Laya-21/XIMO_2.0/Media/img1.jpg

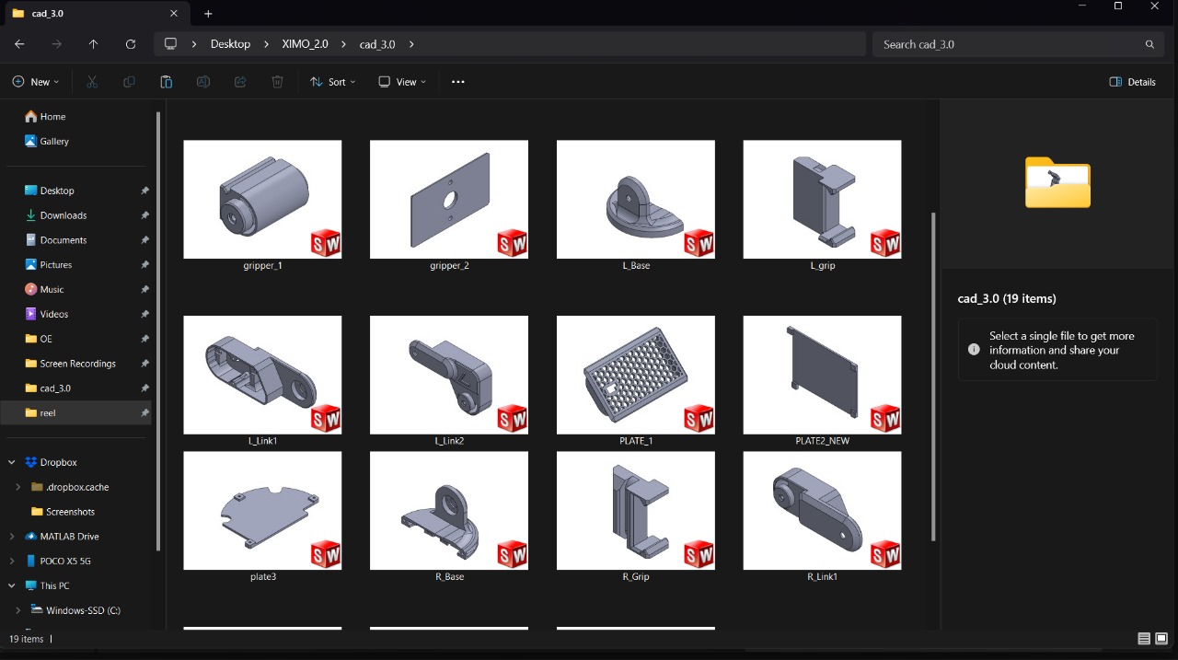
Media/img1.jpg
