Laya-21/XIMO_2.0/Media/img3.jpg

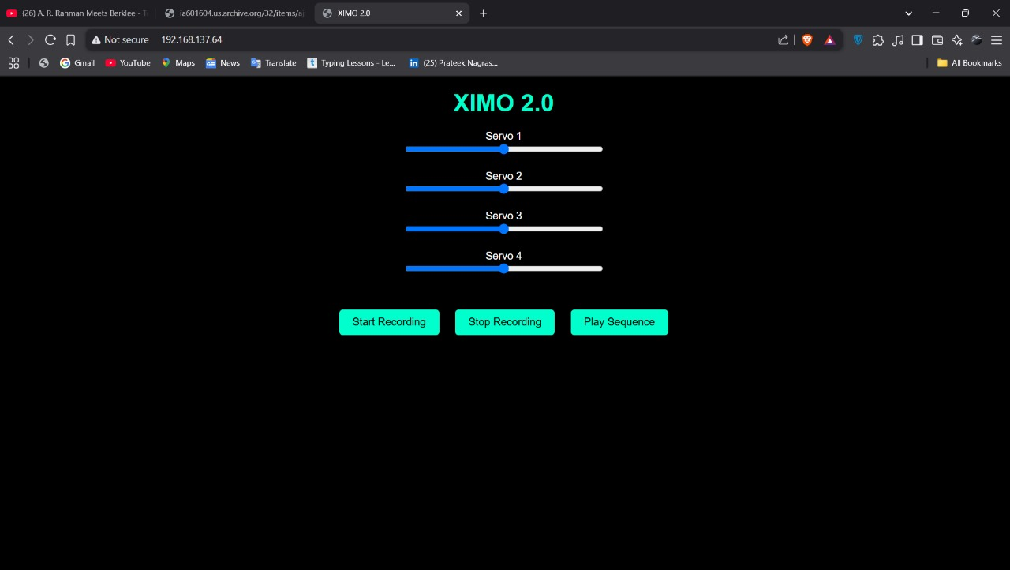
Media/img3.jpg
