Laya-21/XIMO_2.0/Media/img4.png

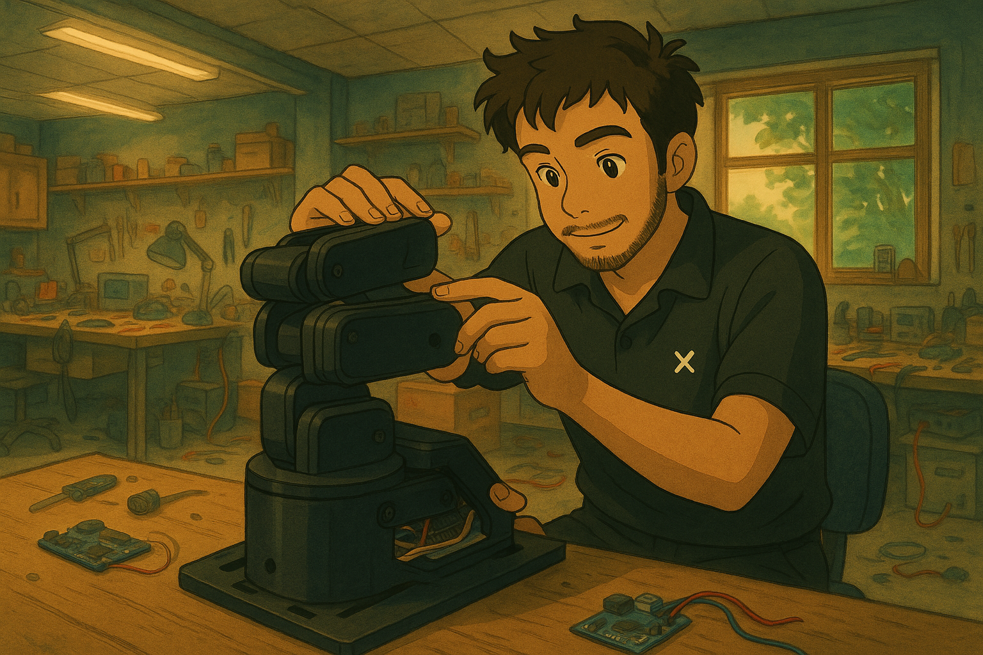
Media/img4.png
