Laya-21/XIMO_2.0/Media/img5.png

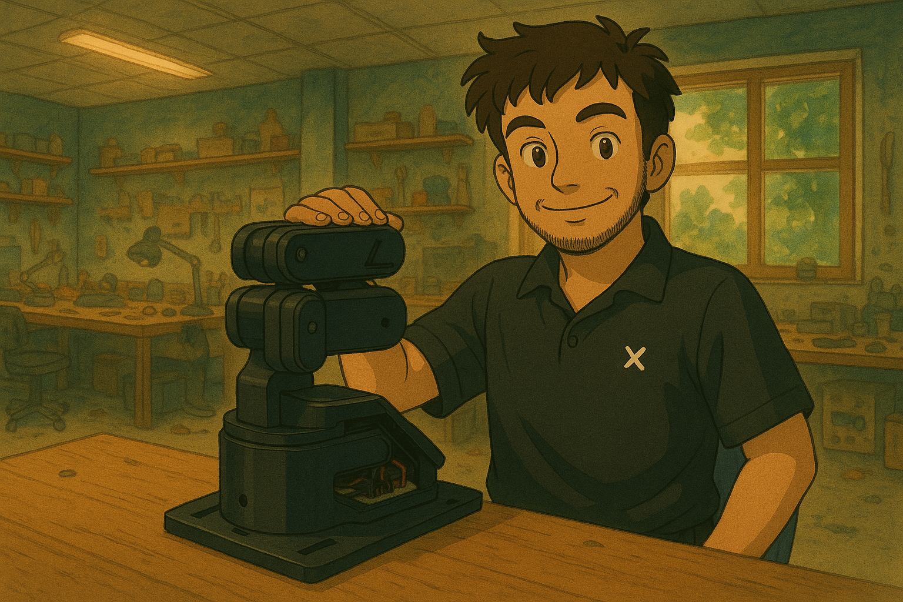
Media/img5.png
