Laya-21/XIMO_2.0/Media/IMG7.png

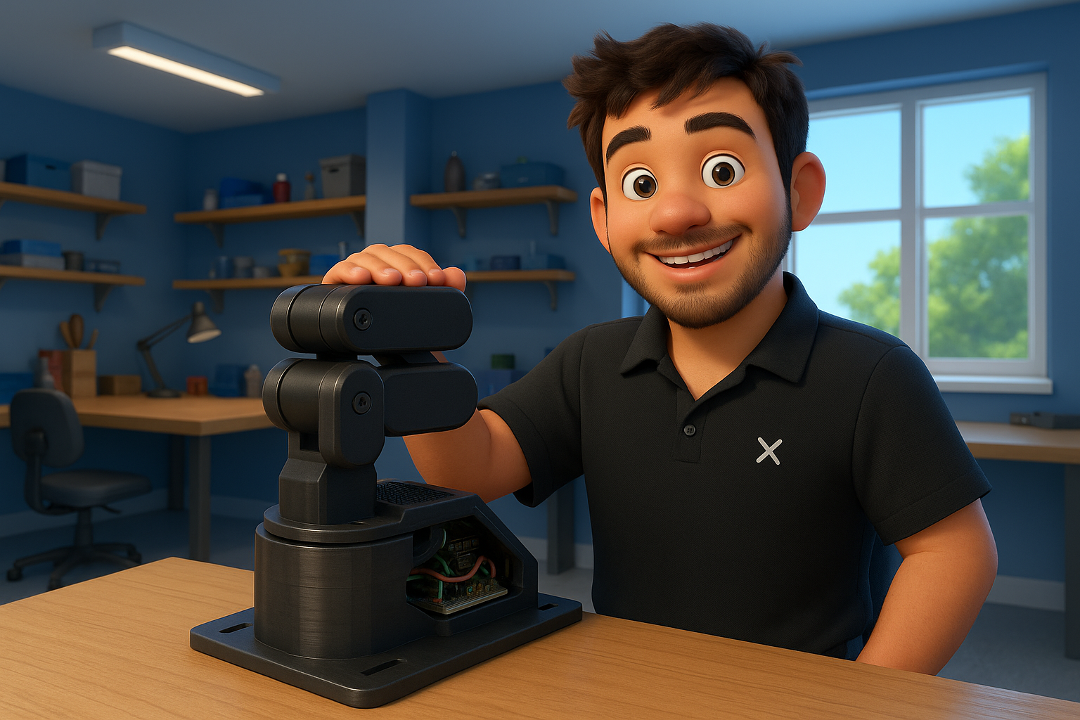
Media/IMG7.png
