Laya-21/XIMO_2.0/Media/img9.png

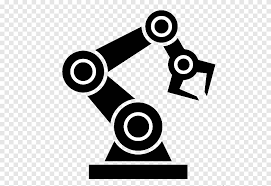
Media/img9.png
