Laya-21/XIMO_2.0/Media/img10.jpg

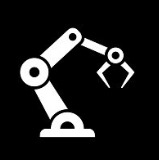
Media/img10.jpg
