Laya-21/XIMO_2.0/cad/PLATE2_NEW.SLDPRT

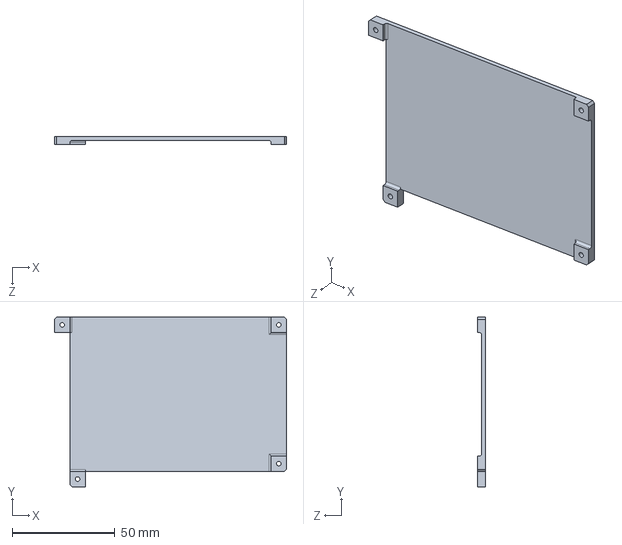
[picture p26: CAD file, 2025-04-26]
cad/PLATE2_NEW.SLDPRT
113.0 x 82.6 x 4.00 mm
