Laya-21/XIMO_2.0/cad/prop.SLDPRT

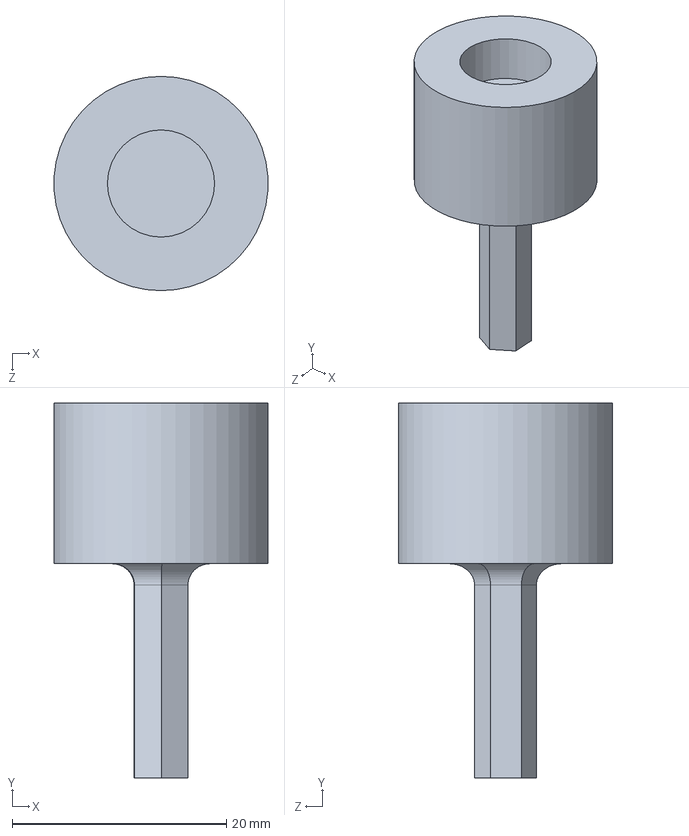
[picture p27: CAD file, 2025-04-26]
cad/prop.SLDPRT
20.0 x 35.0 x 20.0 mm
