Laya-21/XIMO_2.0/CODE/OLED/OLED.ino

#include <Wire.h>
#include <Adafruit_GFX.h>
#include <Adafruit_SSD1306.h>

#define SCREEN_WIDTH 128
#define SCREEN_HEIGHT 64

// If using I2C:
#define OLED_RESET    -1 // Reset pin # (or -1 if sharing Arduino reset pin)
Adafruit_SSD1306 display(SCREEN_WIDTH, SCREEN_HEIGHT, &Wire, OLED_RESET);

void setup() {
  // initialize with the I2C addr 0x3C (common)
  if(!display.begin(SSD1306_SWITCHCAPVCC, 0x3C)) { 
    Serial.println(F("SSD1306 allocation failed"));
    for(;;); // Don't proceed, loop forever
  }

  display.clearDisplay();
  display.setTextSize(2);             // Text size: 1-3 are good
  display.setTextColor(SSD1306_WHITE); 
  display.setCursor(10, 25);          // X=10, Y=25
  display.println("Laya");
  display.display();
}

void loop() {
  // Nothing needed here
}
